Supercookiegaming/6502-ROR-Test-Board/EDA Files/KiCad 9 6502 ROR Test Board V2.0T/DIP-14_W7.62mm.step

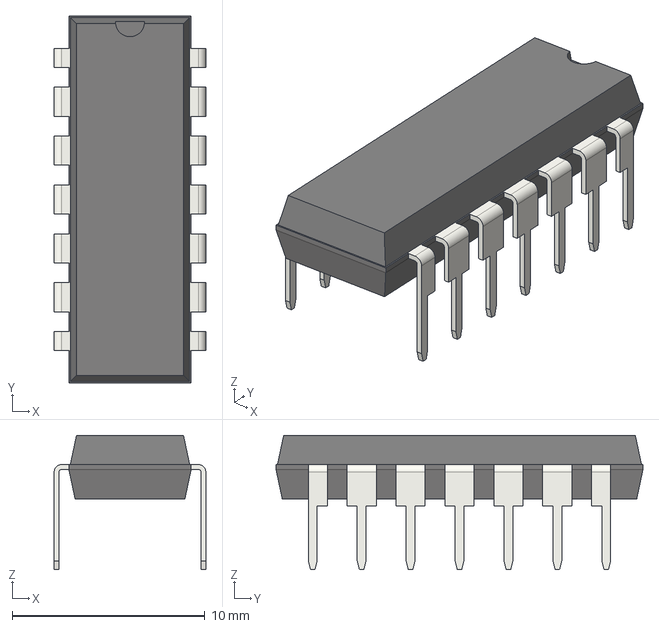
[picture p16: CAD file, 2025-04-16]
EDA Files/KiCad 9 6502 ROR Test Board V2.0T/DIP-14_W7.62mm.step
7.87 x 19.1 x 6.98 mm
