Supercookiegaming/6502-ROR-Test-Board/EDA Files/KiCad 9 6502 ROR Test Board V2.0S/228-1277-00-0602J.STEP

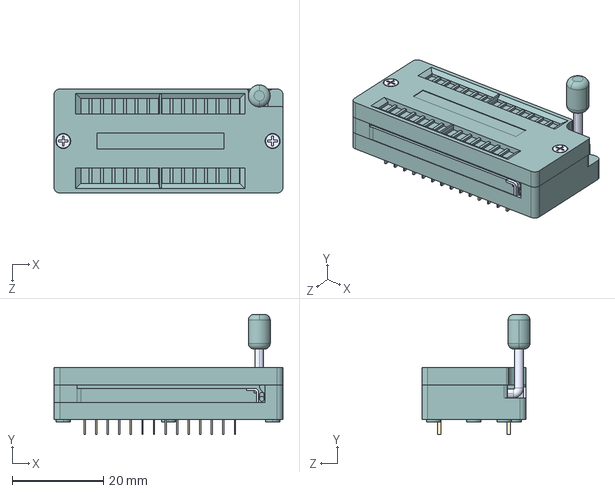
[picture p17: CAD file, 2025-04-16]
EDA Files/KiCad 9 6502 ROR Test Board V2.0S/228-1277-00-0602J.STEP
50.3 x 26.4 x 23.7 mm
