Supercookiegaming/6502-ROR-Test-Board/EDA Files/KiCad 9 6502 ROR Test Board V2.0T/240-1280-00-0602J.STEP

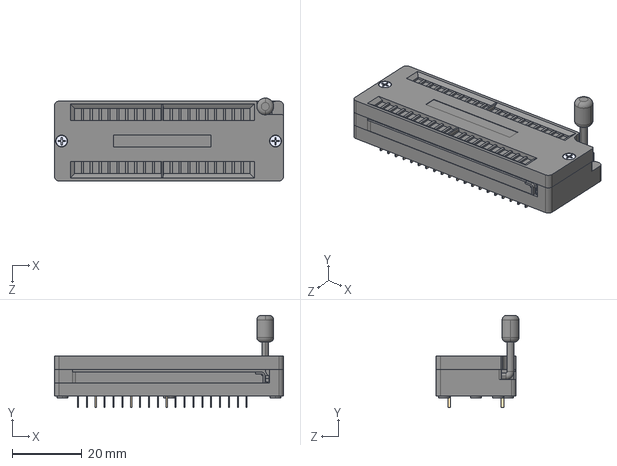
[picture p18: CAD file, 2025-04-16]
EDA Files/KiCad 9 6502 ROR Test Board V2.0T/240-1280-00-0602J.STEP
65.5 x 26.4 x 23.7 mm
